pdaxrom/p601zero-plus/pal_video.vhd

library IEEE;
use IEEE.STD_LOGIC_1164.ALL;
use IEEE.NUMERIC_STD.ALL;

entity pal_video is
    Port(clk				: in  std_logic;
			line_visible	: out std_logic;
			line_even		: out std_logic;
			sync			: out std_logic;
			hsync			: out std_logic;
			colorin			: in std_logic_vector(5 downto 0);
			color			: out std_logic_vector(5 downto 0);
			cntHS			: out unsigned(8 downto 0);
			cntVS			: out unsigned(8 downto 0));
end pal_video;

architecture Behavioral of pal_video is

	signal hcount		: unsigned(8 downto 0) := (others => '0');
	signal vcount		: unsigned(8 downto 0) := (others => '0');
	
	signal in_vbl		: std_logic;
	signal screen_sync: std_logic;
	signal vbl_sync	: std_logic;
	
	signal even : std_logic := '1';
	
	type tpalette is array(7 downto 0) of std_logic_vector(5 downto 0);
	signal palette	: tpalette := (
			 0=>"111100",
			 1=>"001111",
			 2=>"001100",
			 3=>"110011",
			 4=>"110000",
			 5=>"000011",
			 6=>"000000",
			 7=>"111111");

begin

	process (clk)
	begin
		if rising_edge(clk) then
			if hcount=511 then
				hcount <= (others => '0');
				if vcount=311 then
					vcount <= (others=>'0');
					even <= not even;
				else
					vcount <= vcount + 1;
				end if;
			else
				hcount <= hcount + 1;
			end if;
		end if;
	end process;
	
	process (hcount)
	begin
		if hcount<37 then
			screen_sync <= '0';
		else
			screen_sync <= '1';
		end if;
	end process;
	
	process (vcount)
	begin
		if vcount>=5 and vcount<309 then
			in_vbl <= '0';
		else
			in_vbl <= '1';
		end if;
	end process;
	
	line_visible	<= not in_vbl;
	line_even		<= not vcount(0);
	hsync			<= not screen_sync;
	
	cntHS <= hcount;
	cntVS <= vcount;
	
	process (vcount,hcount)
	begin
		if vcount<2 then
			if hcount<240 or (hcount>=256 and hcount<496) then
				vbl_sync <= '0';
			else
				vbl_sync <= '1';
			end if;
		elsif vcount=2 then
			if hcount<240 or (hcount>=256 and hcount<272) then
				vbl_sync <= '0';
			else
				vbl_sync <= '1';
			end if;
		else
			if hcount<16 or (hcount>=256 and hcount<272) then
				vbl_sync <= '0';
			else
				vbl_sync <= '1';
			end if;
		end if;
	end process;
	
	process (in_vbl,screen_sync,vbl_sync)
	begin
		if in_vbl='1' then
			sync <= vbl_sync;
		else
			sync <= screen_sync;
		end if;
	end process;
	
	
	
	process(in_vbl,hcount,vcount,palette)
	begin
		if in_vbl='1' or hcount<(37+12+18+17) or hcount>=(37+12+18+17+416) then
			color <= "000000";
		else
			color <= colorin;
		end if;
	end process;
	
end Behavioral;
